apic-ai/jetson-tree/resources/images/technical_drawings/02.PNG

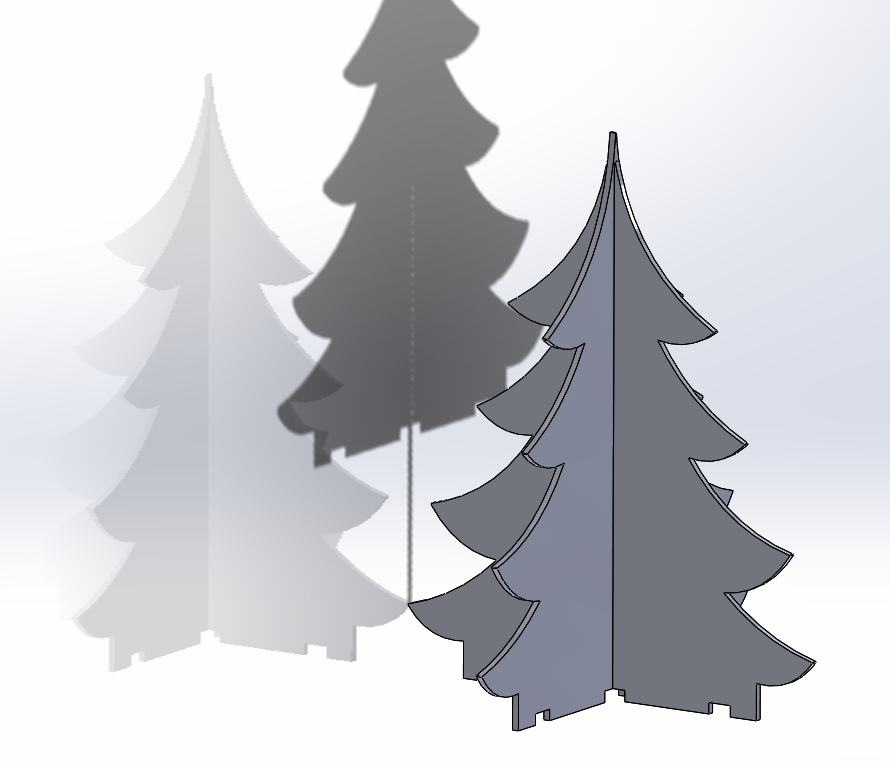
resources/images/technical_drawings/02.PNG
