apic-ai/jetson-tree/resources/images/technical_drawings/03.PNG

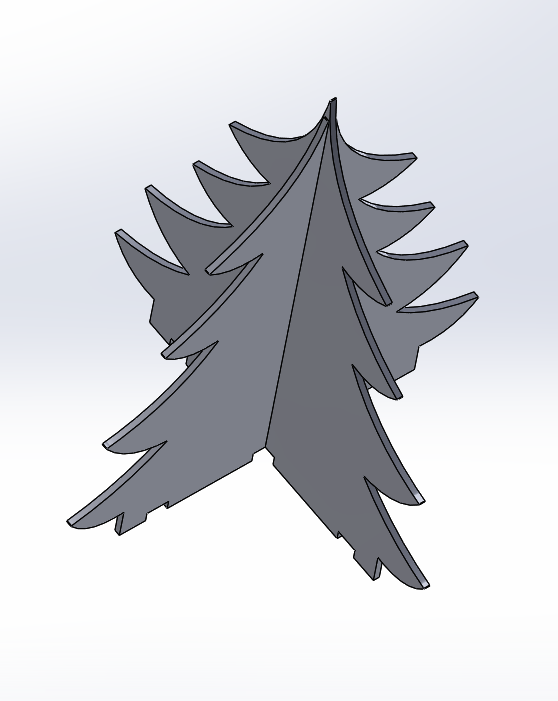
resources/images/technical_drawings/03.PNG
