apic-ai/jetson-tree/resources/images/technical_drawings/04.PNG

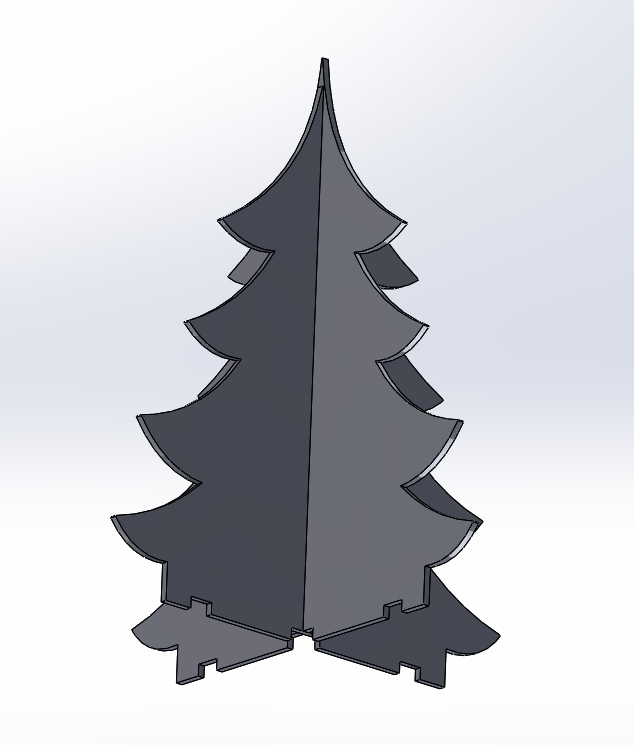
resources/images/technical_drawings/04.PNG
